ocdpoptart/keyguy/keyguy2.0/output/outlines/raw.dxf

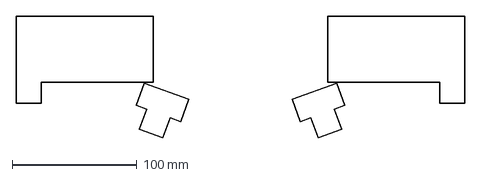
[picture p16: CAD file, 2024-09-17]
keyguy2.0/output/outlines/raw.dxf
360.0 x 97.5 mm
