ocdpoptart/keyguy/keyguy2.0/output/outlines/board2.dxf

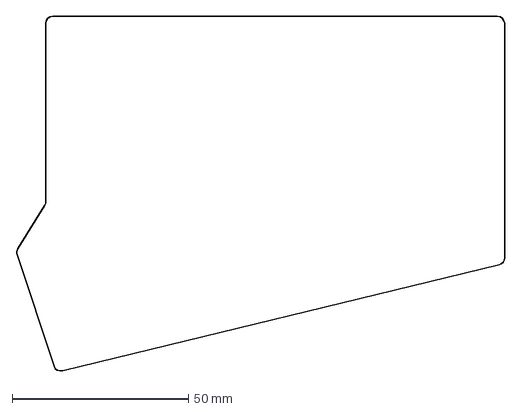
[picture p18: CAD file, 2024-09-17]
keyguy2.0/output/outlines/board2.dxf
138.3 x 100.7 mm
