ocdpoptart/keyguy/keyguy2.0/output/outlines/mounting.dxf

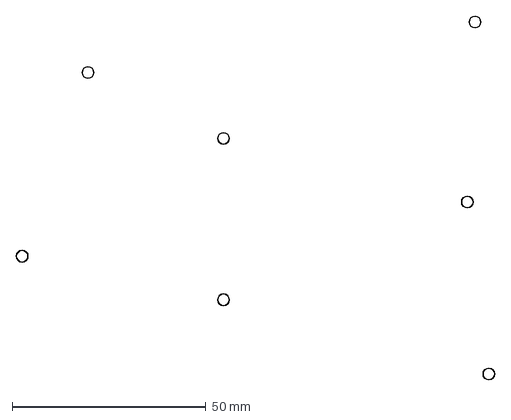
[picture p19: CAD file, 2024-09-17]
keyguy2.0/output/outlines/mounting.dxf
123.6 x 93.9 mm
