ocdpoptart/keyguy/keyguy2.0/output/outlines/mounting2.dxf

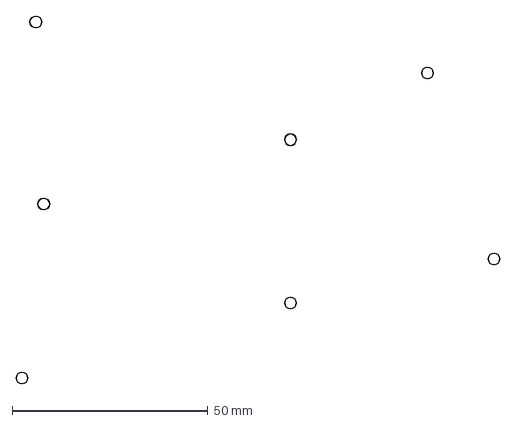
[picture p20: CAD file, 2024-09-17]
keyguy2.0/output/outlines/mounting2.dxf
123.6 x 93.9 mm
