ocdpoptart/keyguy/keyguy2.0/output/outlines/xlboard.dxf

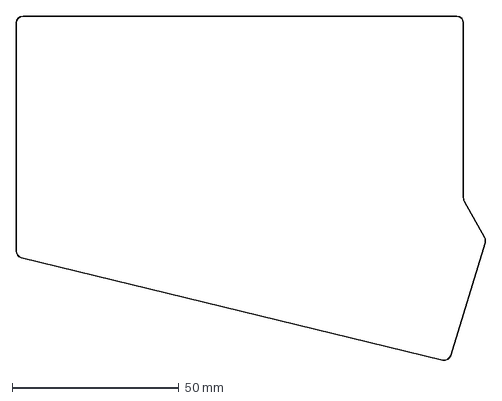
[picture p21: CAD file, 2024-09-17]
keyguy2.0/output/outlines/xlboard.dxf
140.6 x 103.3 mm
