ocdpoptart/keyguy/keyguy2.0/output/outlines/combo2.dxf

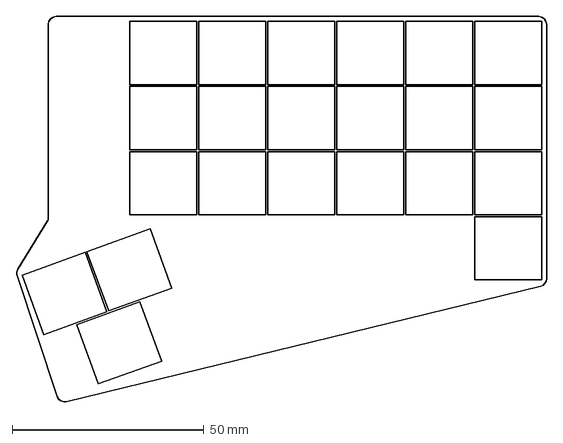
[picture p22: CAD file, 2024-09-17]
keyguy2.0/output/outlines/combo2.dxf
138.3 x 100.7 mm
